takashicompany/meicb/images/build/IMG_1972.jpg

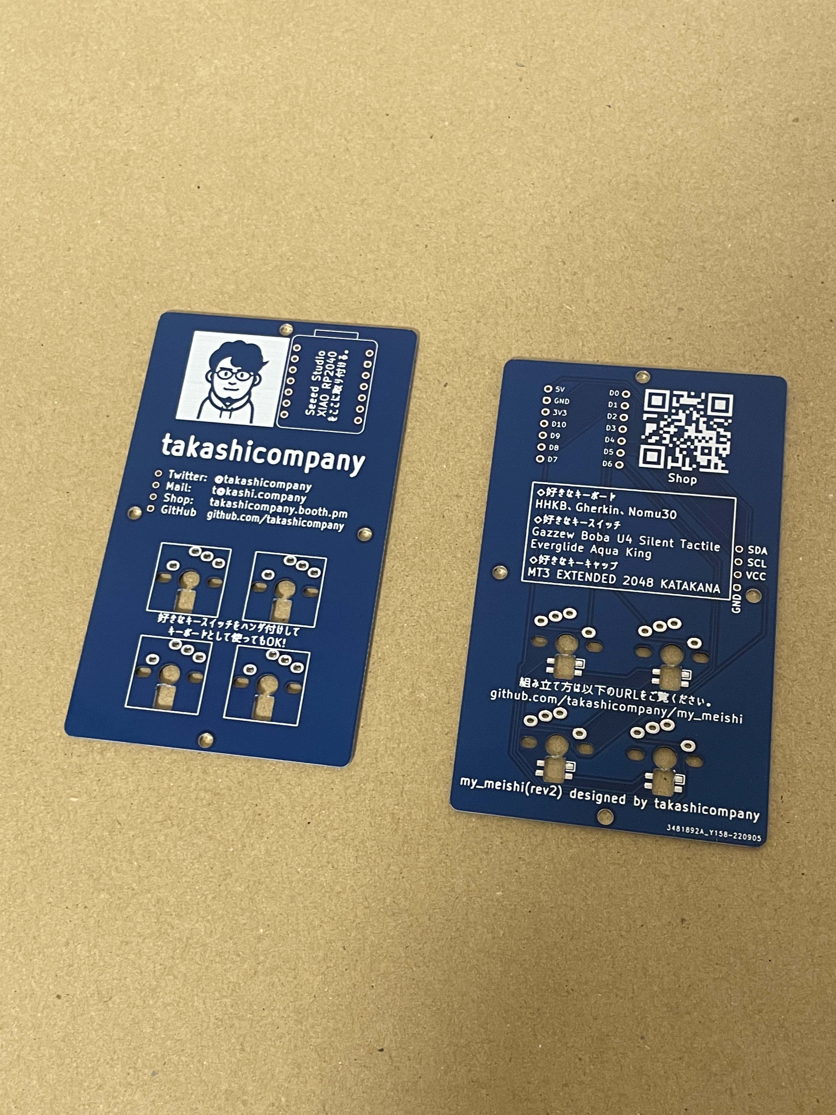
images/build/IMG_1972.jpg
