takashicompany/meicb/images/build/IMG_1979.jpg

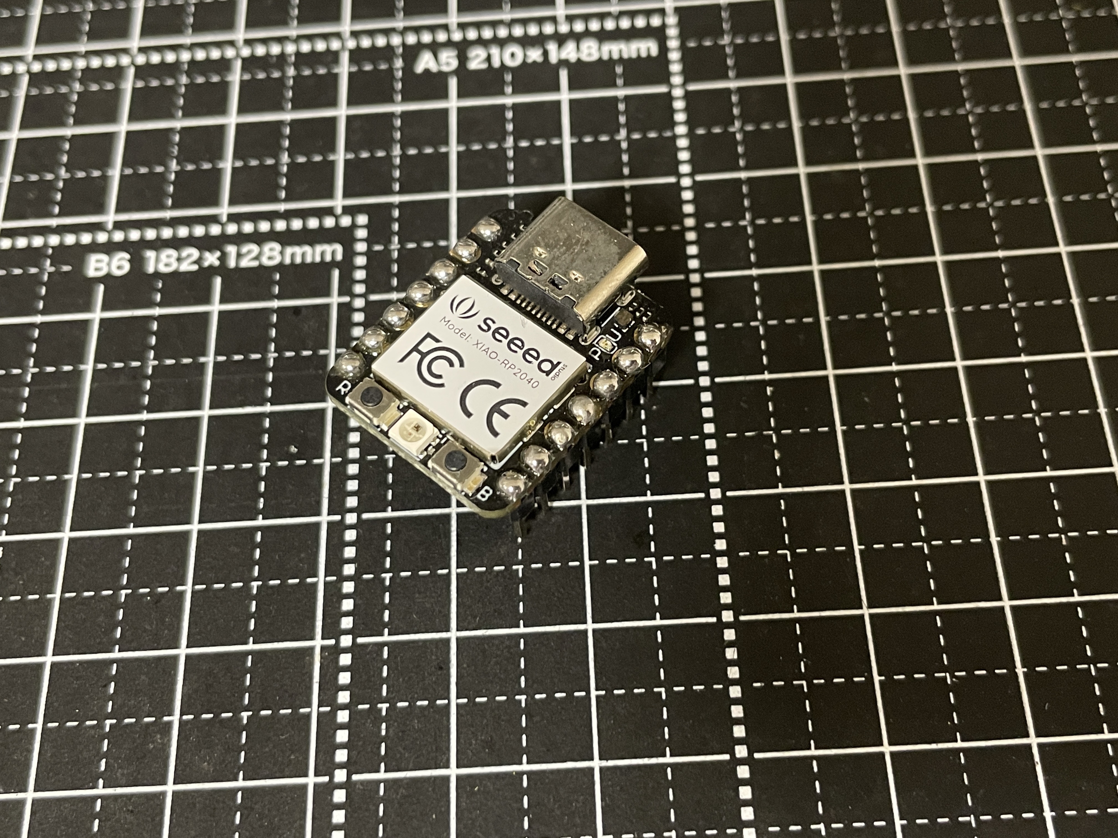
images/build/IMG_1979.jpg
