takashicompany/meicb/images/build/IMG_1984.jpg

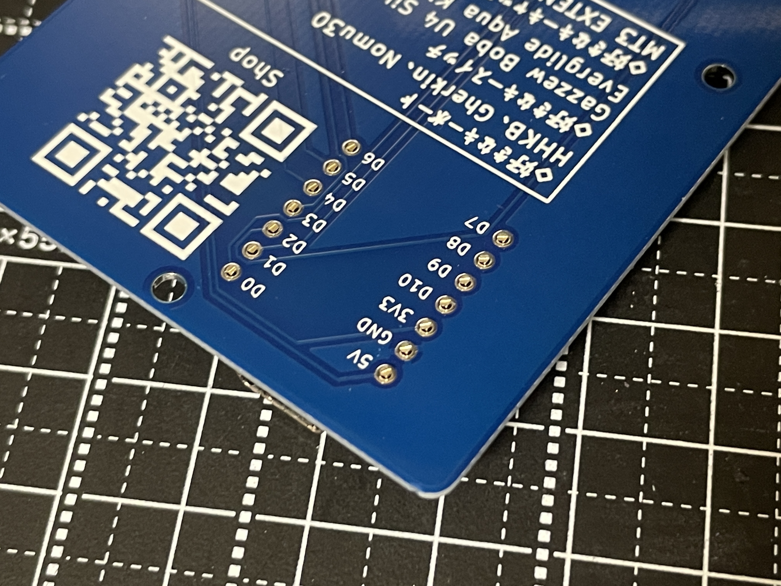
images/build/IMG_1984.jpg
