takashicompany/meicb/images/build/IMG_1989.jpg

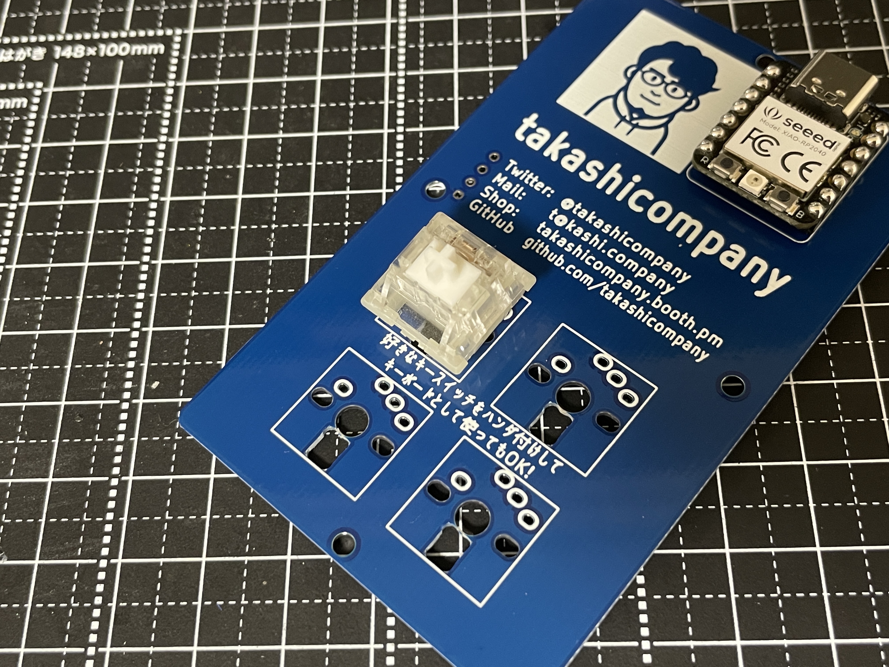
images/build/IMG_1989.jpg
