takashicompany/meicb/images/build/IMG_1990.jpg

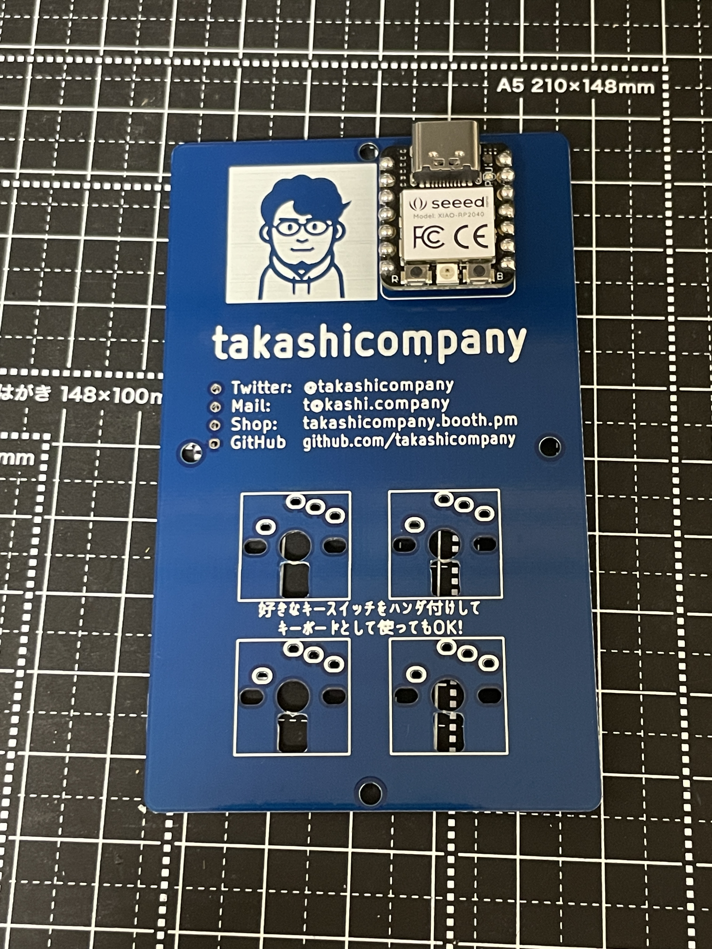
images/build/IMG_1990.jpg
