takashicompany/meicb/images/build/IMG_1991.jpg

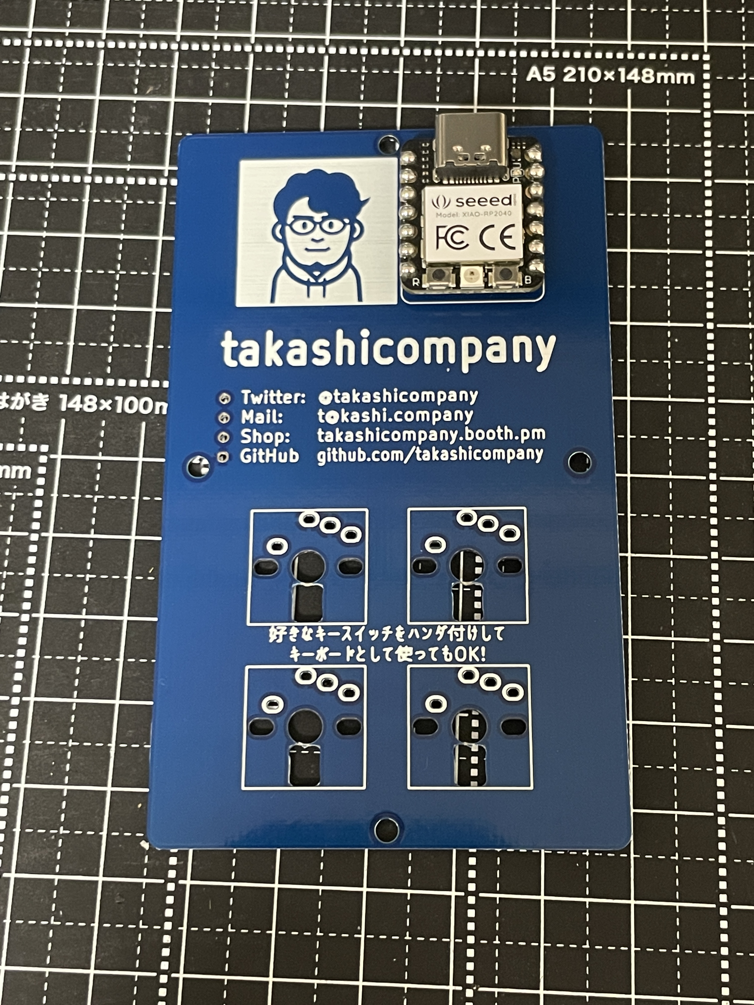
images/build/IMG_1991.jpg
