takashicompany/meicb/images/build/IMG_1992.jpg

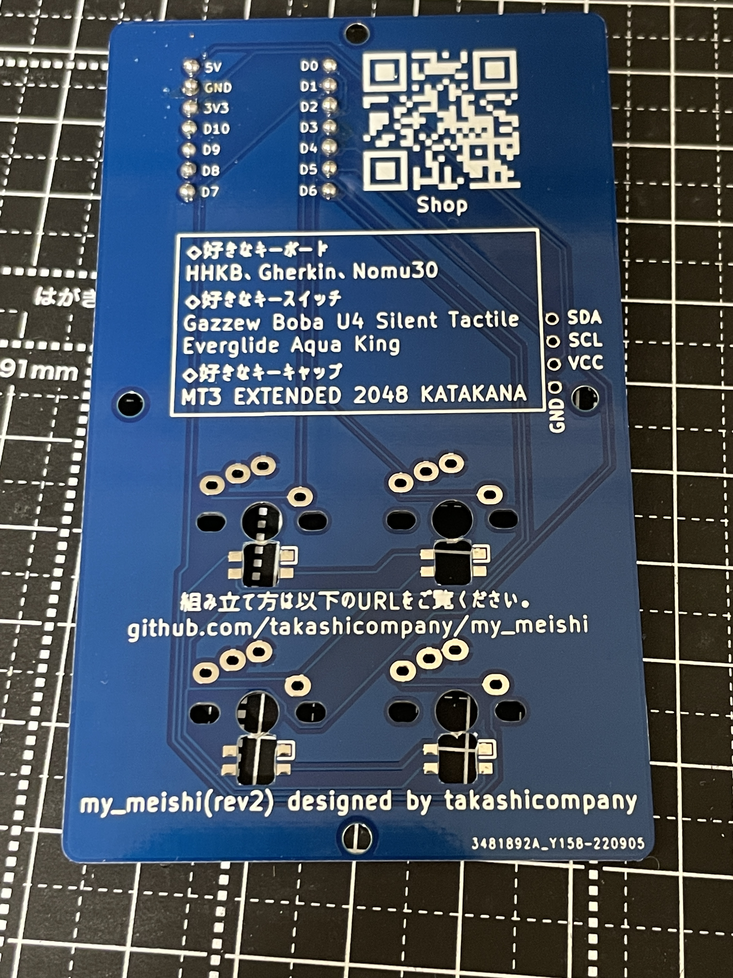
images/build/IMG_1992.jpg
