takashicompany/meicb/images/build/IMG_1993.jpg

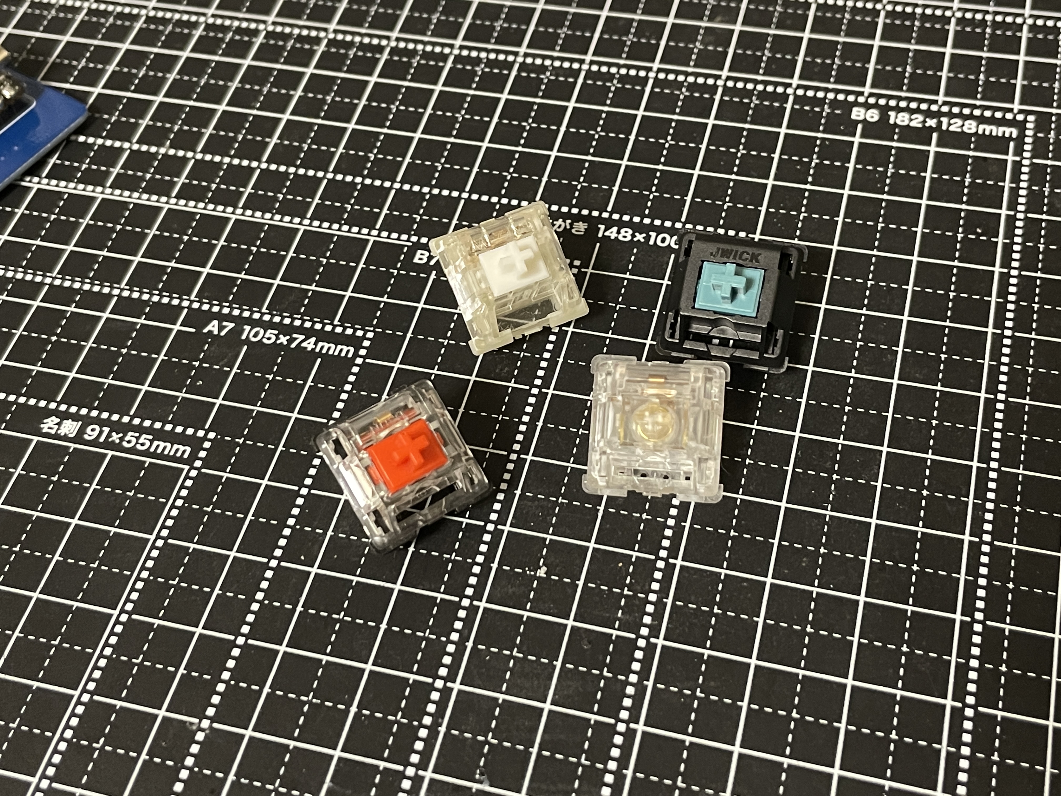
images/build/IMG_1993.jpg
