takashicompany/meicb/images/build/IMG_1994.jpg

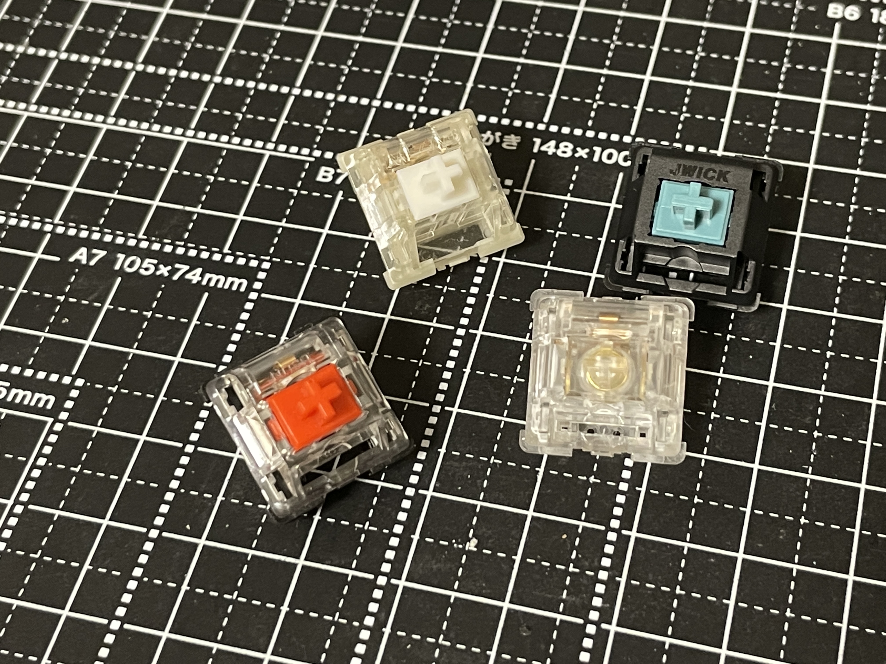
images/build/IMG_1994.jpg
