takashicompany/meicb/images/build/IMG_2001.jpg

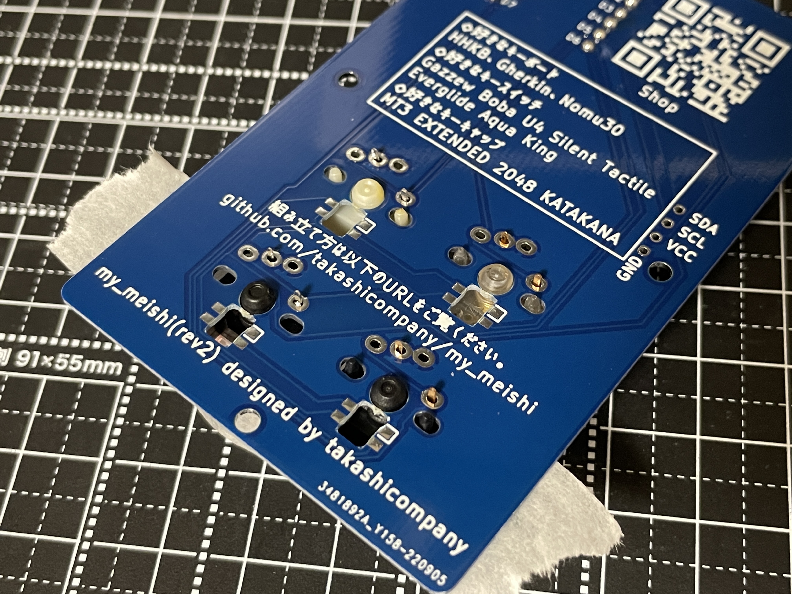
images/build/IMG_2001.jpg
