takashicompany/meicb/images/build/IMG_2004.jpg

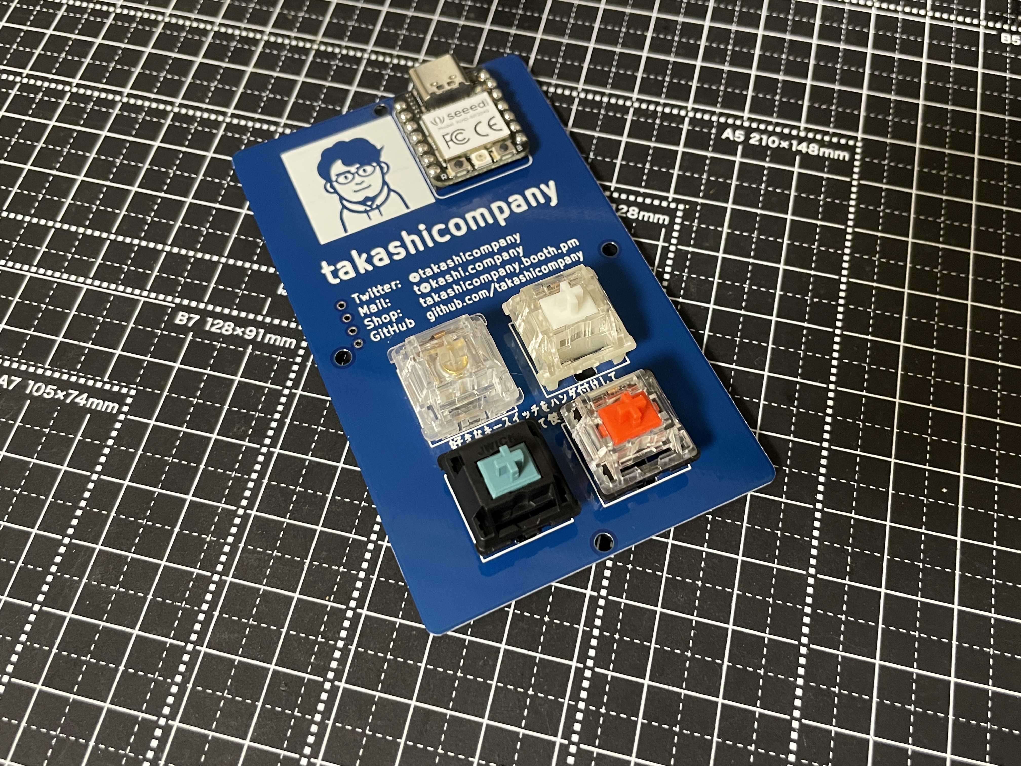
images/build/IMG_2004.jpg
