takashicompany/meicb/images/build/IMG_2006.jpg

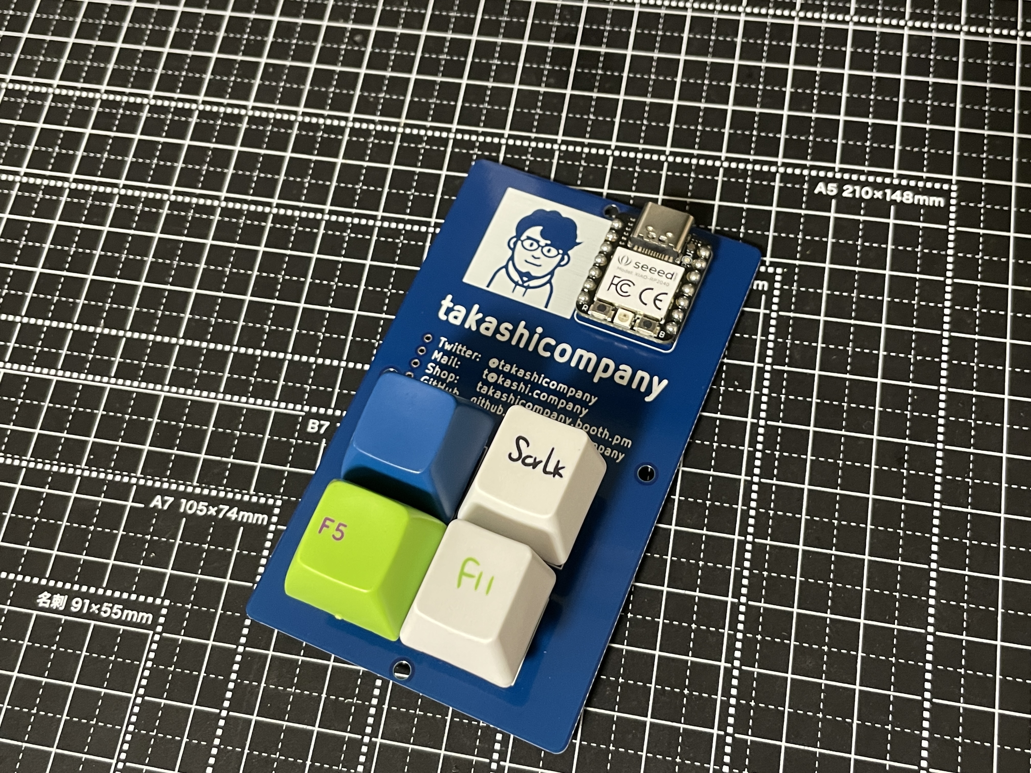
images/build/IMG_2006.jpg
