takashicompany/meicb/images/build/IMG_2007.jpg

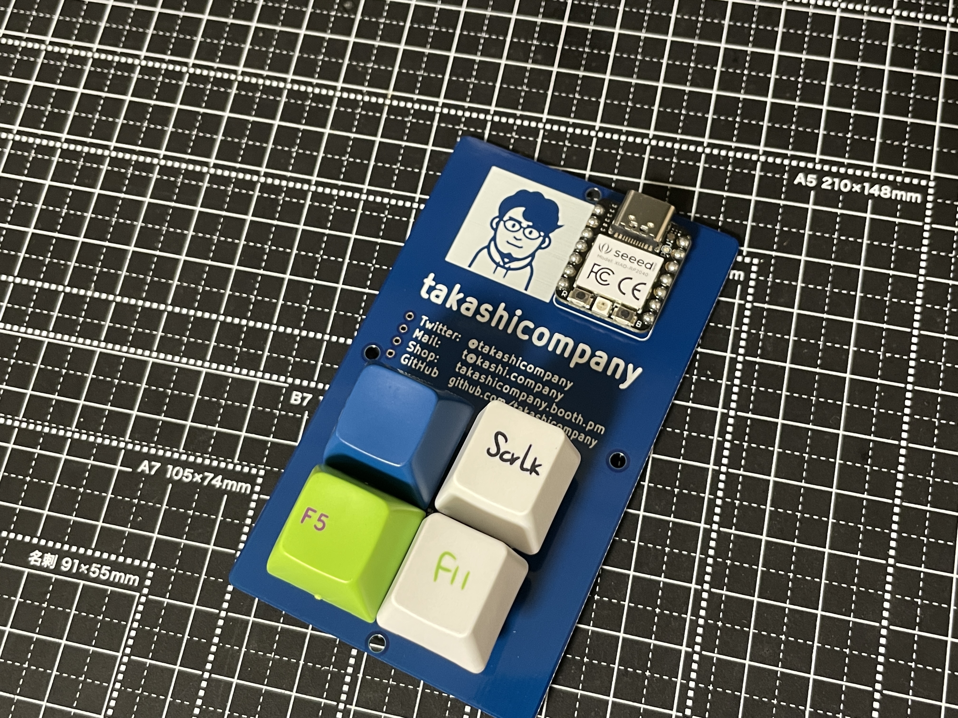
images/build/IMG_2007.jpg
